AllAboutEE/Analog-Inputs-For-ESP8266/Software/ESP8266-Arduino-Library-For-MCP3021/AllAboutEE_MCP3021.h

#ifndef _ALLABOUTEE_MCP3021_H
#define _ALLABOUTEE_MCP3021_H

#include <Wire.h>

namespace AllAboutEE
{
    class MCP3021
    {
    public:
        void begin(int sda, int scl);
		uint16_t read(int deviceId);
        float read(int deviceId, float vdd); //returns analog value
    private:
        static const int MCP3021_I2C_ADDRESS = 0x48;
    };
}

#endif
